AntonVonDelta/AutoGarden/Schematica/Autogradina.kicad_sch

## KiCad design Schematica/Autogradina.kicad_sch (2022-01-23)

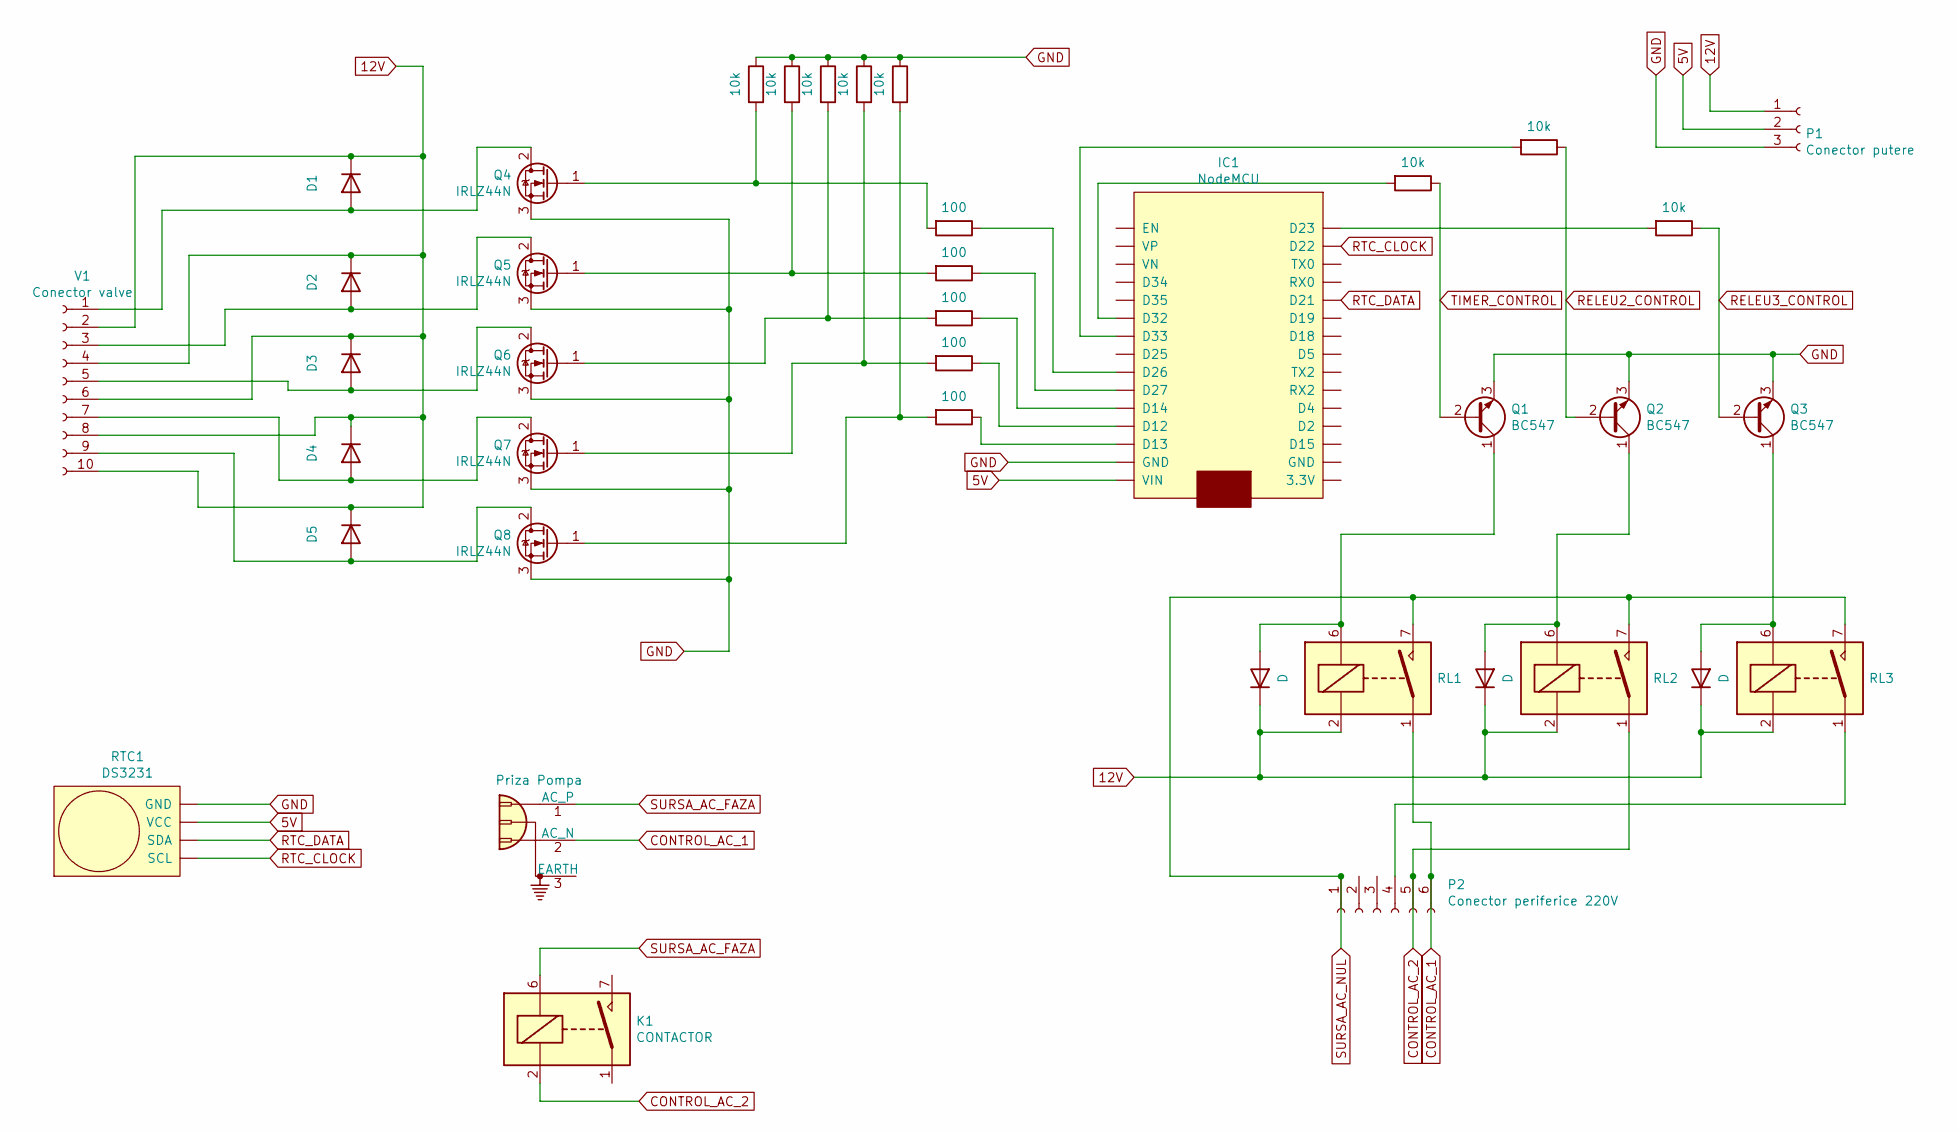
[picture p3: schematic Autogradina.kicad_sch]

Parts:
D1, D2, D3, D4, D5, D6, D7, D8: D
IC1: NodeMCU
J1: Priza Pompa
K1: CONTACTOR; Relay_StandexMeder_DIP_LowProfile
P1: Conector putere
P2: Conector periferice 220V
Q1, Q2, Q3: BC547; TO-92_Inline
Q4, Q5, Q6, Q7, Q8: IRLZ44N; TO-220-3_Vertical
R1, R2, R3, R4, R5, R11, R12, R13: 10k
R6, R7, R8, R9, R10: 100
RL1, RL2, RL3: DIPxx-1Axx-11x; Relay_StandexMeder_DIP_LowProfile
RTC1: DS3231
V1: Conector valve

Connections:
5V: IC1.4 (VIN), P1.2, RTC1.3 (VCC)
12V: D1.1 (K), D2.1 (K), D3.1 (K), D4.1 (K), D5.1 (K), D6.1 (K), D7.1 (K), D8.1 (K), P1.1, RL1.2, RL2.2, RL3.2, V1.2, V1.4, V1.6, V1.8, V1.10
CONTROL_AC_1: J1.2 (AC_N), P2.6, RL1.1, RL1.14
CONTROL_AC_2: K1.2, P2.5, RL2.1, RL2.14
GND: IC1.9 (GND), P1.3, Q1.3 (E), Q2.3 (E), Q3.3 (E), Q4.3 (S), Q5.3 (S), Q6.3 (S), Q7.3 (S), Q8.3 (S), R1.1, R2.1, R3.1, R4.1, R5.1, RTC1.4 (GND)
unnamed: D1.2 (A), Q4.2 (D), V1.1
unnamed: D2.2 (A), Q5.2 (D), V1.3
unnamed: D3.2 (A), Q6.2 (D), V1.5
unnamed: D4.2 (A), Q7.2 (D), V1.7
unnamed: D5.2 (A), Q8.2 (D), V1.9
unnamed: D6.2 (A), Q1.1 (C), RL1.6
unnamed: D7.2 (A), Q2.1 (C), RL2.6
unnamed: D8.2 (A), Q3.1 (C), RL3.6
unnamed: IC1.1 (D33), R12.2
unnamed: IC1.17 (D32), R11.2
unnamed: IC1.18 (D27), R7.1
unnamed: IC1.19 (D26), R6.1
unnamed: IC1.21 (D23), R13.2
unnamed: IC1.28 (D14), R8.1
unnamed: IC1.29 (D13), R10.1
unnamed: IC1.30 (D12), R9.1
unnamed: K1.1, K1.14
unnamed: K1.7, K1.8
unnamed: P2.4, RL3.1, RL3.14
unnamed: Q4.1 (G), R1.2, R6.2
unnamed: Q5.1 (G), R2.2, R7.2
unnamed: Q6.1 (G), R3.2, R8.2
unnamed: Q7.1 (G), R4.2, R9.2
unnamed: Q8.1 (G), R5.2, R10.2
RELEU2_CONTROL: Q2.2 (B), R12.1
RELEU3_CONTROL: Q3.2 (B), R13.1
RTC_CLOCK: IC1.22 (D22), RTC1.1 (SCL)
RTC_DATA: IC1.23 (D21), RTC1.2 (SDA)
SURSA_AC_FAZA: J1.1 (AC_P), K1.6
SURSA_AC_NUL: P2.1, RL1.7, RL1.8, RL2.7, RL2.8, RL3.7, RL3.8
TIMER_CONTROL: Q1.2 (B), R11.1
